Gabriel220702/Innova-TecNM-2024/COCYTED 2024/Diseño Chaleco .jpg

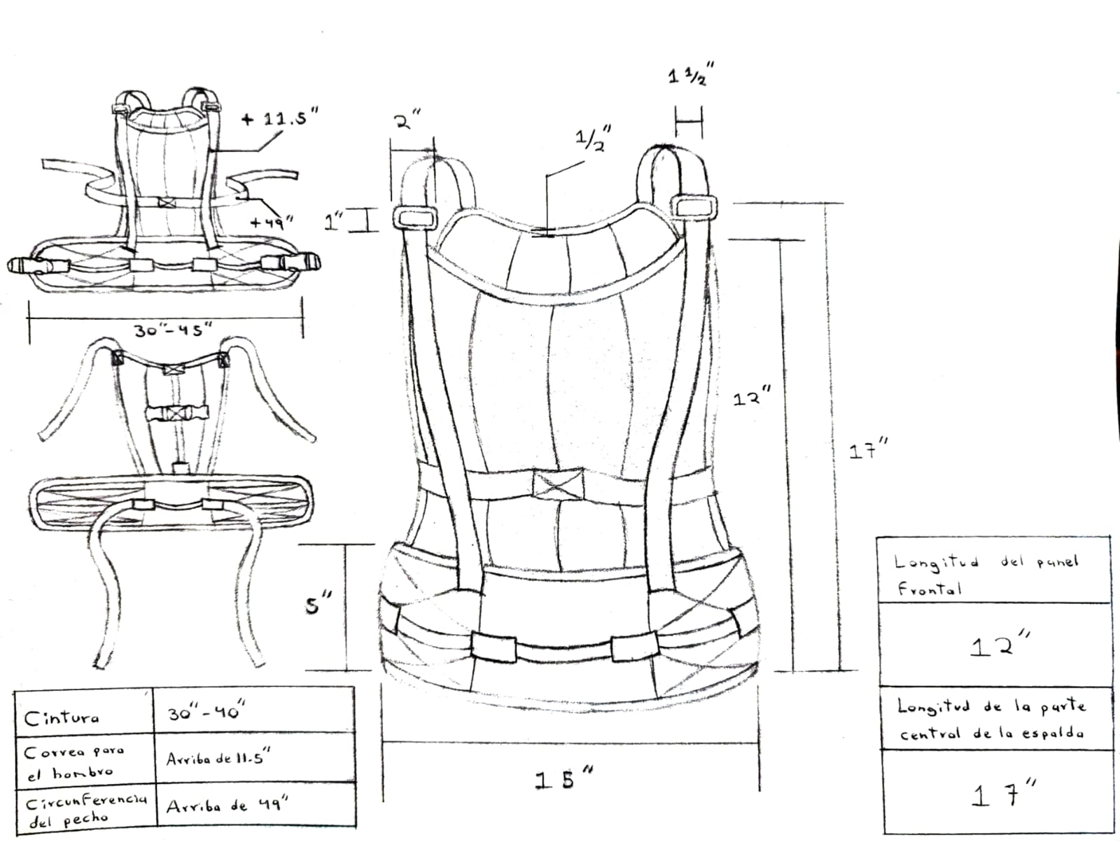
COCYTED 2024/Diseño Chaleco .jpg
