Gabriel220702/Innova-TecNM-2024/Innova TecNM 2024 Etapa Local/Imágenes/Equipo de Trabajo.png

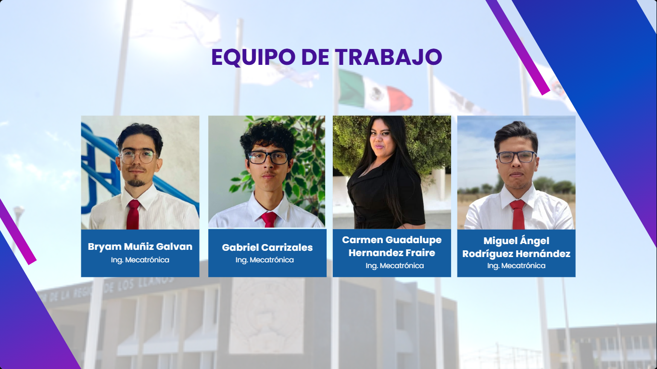
Innova TecNM 2024 Etapa Local/Imágenes/Equipo de Trabajo.png
