Gabriel220702/Innova-TecNM-2024/Innova TecNM 2024 Etapa Local/Imágenes/Estado del Arte.PNG

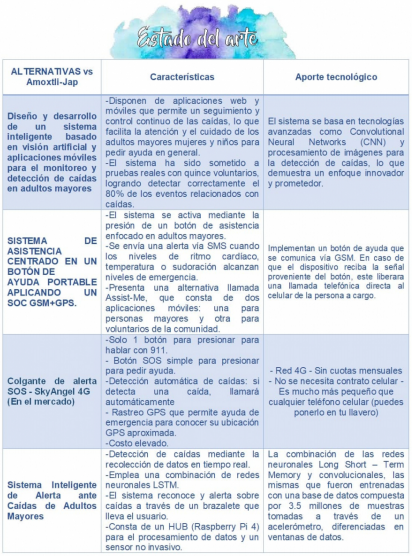
Innova TecNM 2024 Etapa Local/Imágenes/Estado del Arte.PNG
