Gabriel220702/Innova-TecNM-2024/Innova TecNM 2024 Etapa Regional/Carteles/Cartel 1.jpg

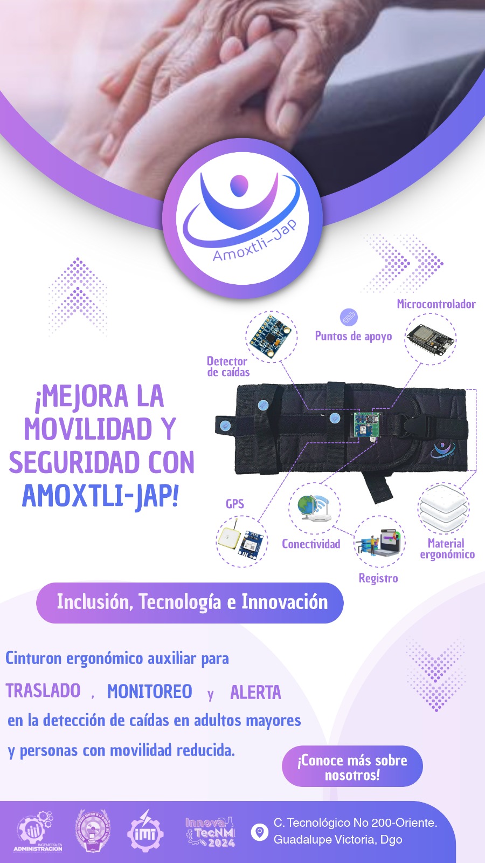
Innova TecNM 2024 Etapa Regional/Carteles/Cartel 1.jpg
