Gabriel220702/Innova-TecNM-2024/Innova TecNM 2024 Etapa Regional/Fotos, Equipo de Trabajo/Bryam.jpg

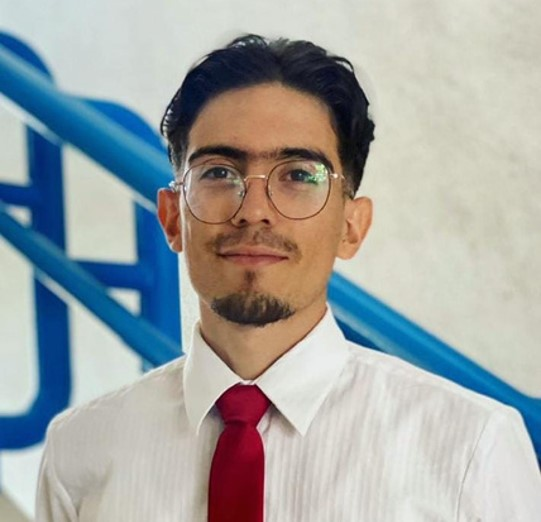
Innova TecNM 2024 Etapa Regional/Fotos, Equipo de Trabajo/Bryam.jpg
