Gabriel220702/Innova-TecNM-2024/Innova TecNM 2024 Etapa Regional/Fotos, Equipo de Trabajo/La_Abril.jpg

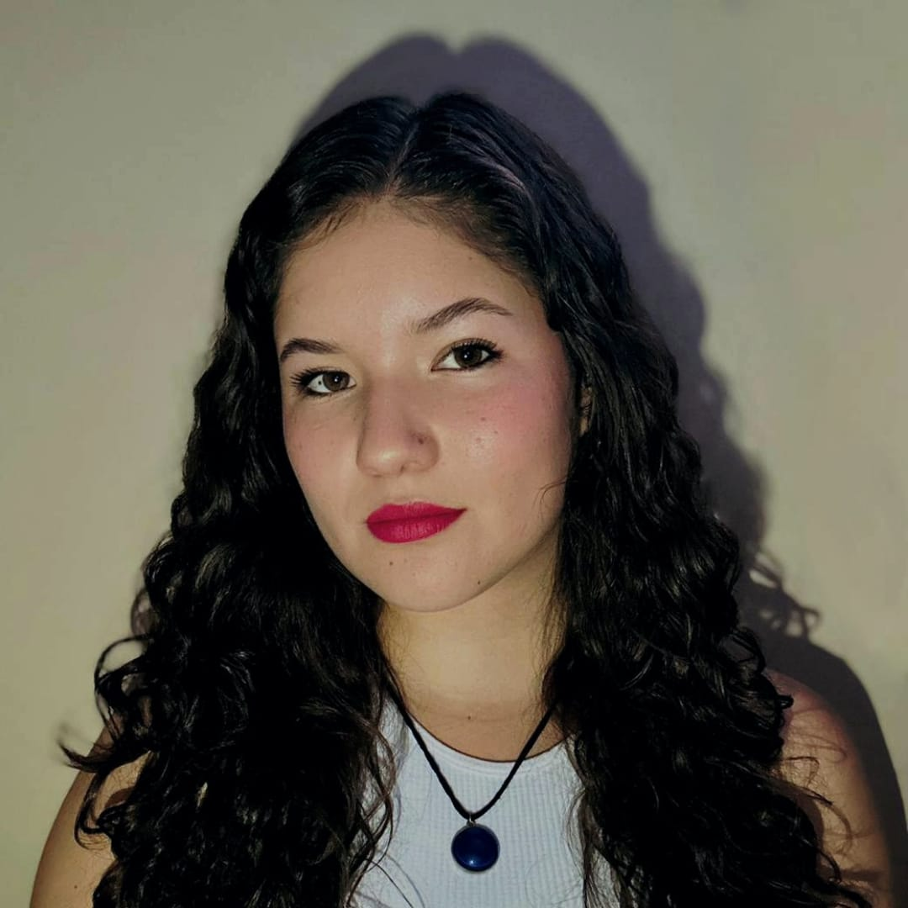
Innova TecNM 2024 Etapa Regional/Fotos, Equipo de Trabajo/La_Abril.jpg
