Gabriel220702/Innova-TecNM-2024/Innova TecNM 2024 Etapa Regional/Galeria de Imagenes, Página Web/Abuelita con Chaleco 3.jpg

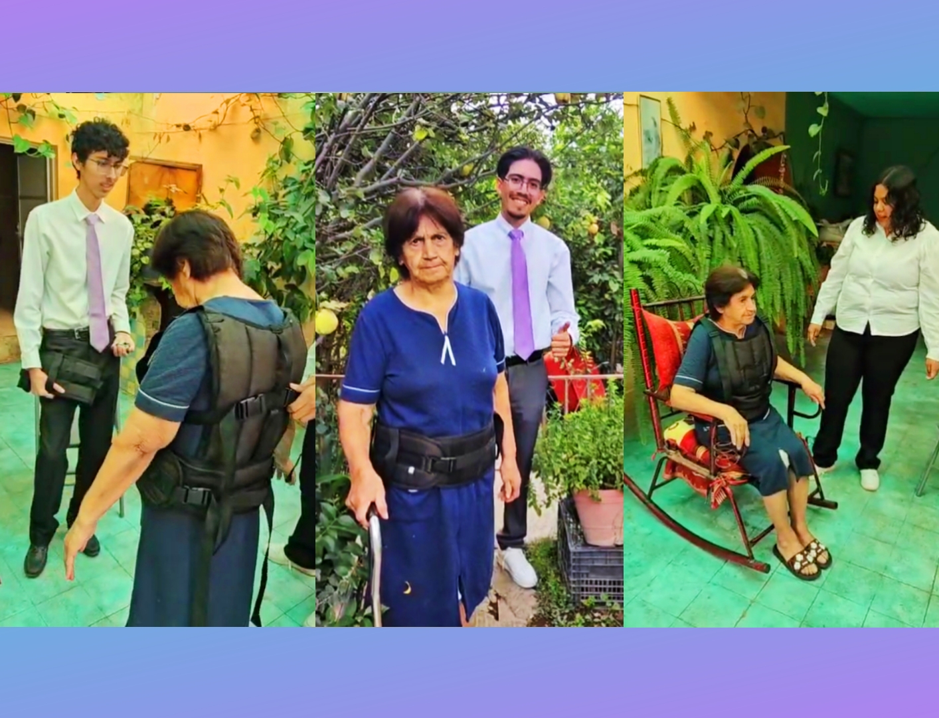
Innova TecNM 2024 Etapa Regional/Galeria de Imagenes, Página Web/Abuelita con Chaleco 3.jpg
