Gabriel220702/Innova-TecNM-2024/Innova TecNM 2024 Etapa Regional/Galeria de Imagenes, Página Web/Cinturón y Chaleco.jpg

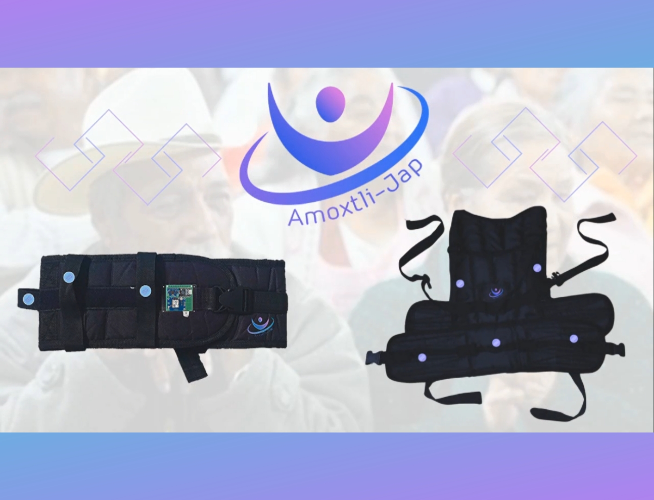
Innova TecNM 2024 Etapa Regional/Galeria de Imagenes, Página Web/Cinturón y Chaleco.jpg
