Gabriel220702/Innova-TecNM-2024/Innova TecNM 2024 Etapa Regional/Galeria de Imagenes, Página Web/Panel de Control.jpg

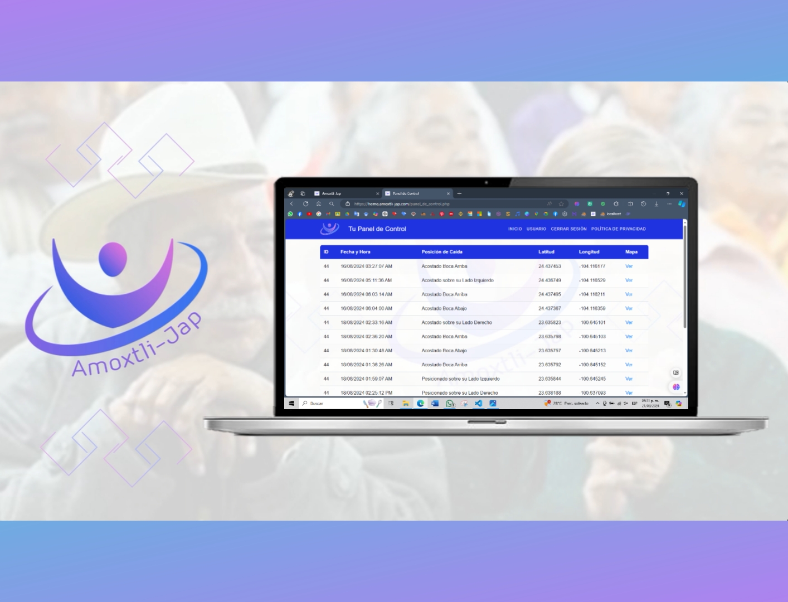
Innova TecNM 2024 Etapa Regional/Galeria de Imagenes, Página Web/Panel de Control.jpg
