Gabriel220702/Innova-TecNM-2024/Innova TecNM 2024 Etapa Regional/Galeria de Imagenes, Página Web/WhatsApp y Google Maps.jpg

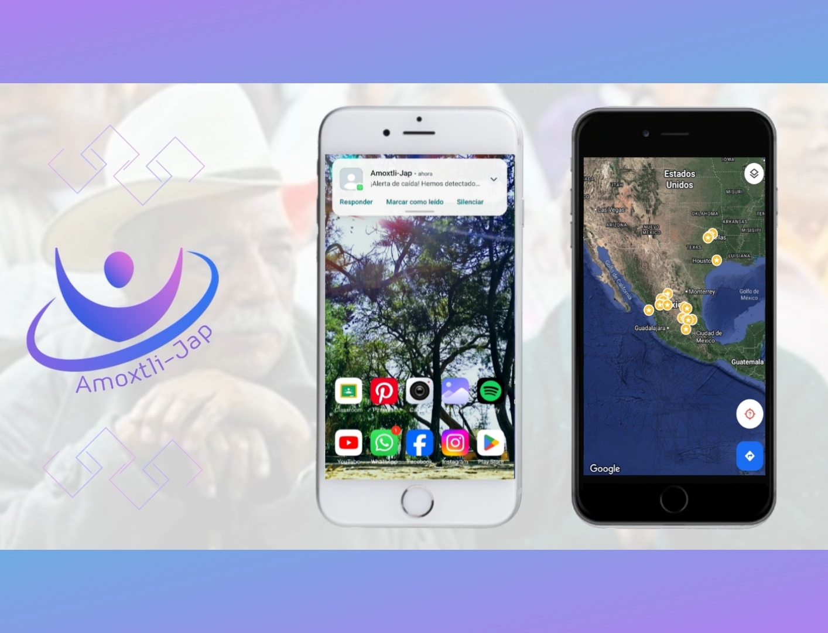
Innova TecNM 2024 Etapa Regional/Galeria de Imagenes, Página Web/WhatsApp y Google Maps.jpg
