Gabriel220702/Innova-TecNM-2024/Innova TecNM 2024 Etapa Regional/Imágenes, Información con Diseño/Cuantificación de Personal.png

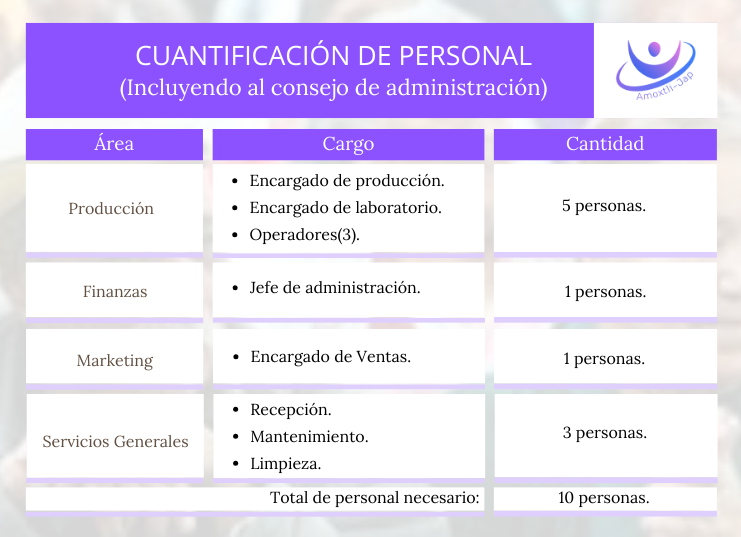
Innova TecNM 2024 Etapa Regional/Imágenes, Información con Diseño/Cuantificación de Personal.png
