Gabriel220702/Innova-TecNM-2024/Innova TecNM 2024 Etapa Regional/Imágenes, Información con Diseño/Descripción de la Innovación.png

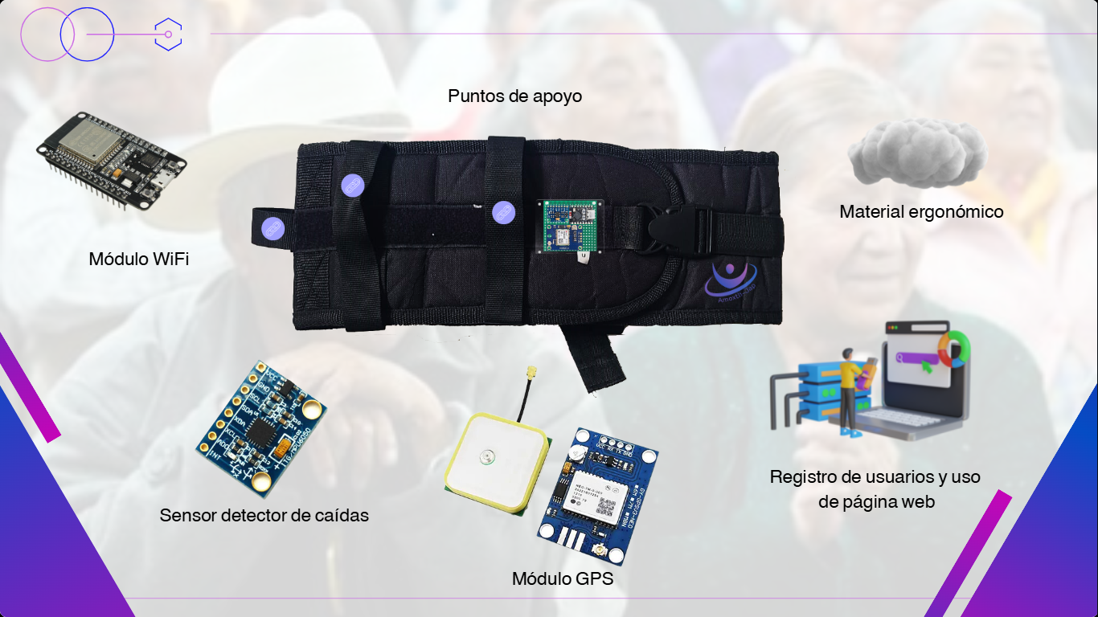
Innova TecNM 2024 Etapa Regional/Imágenes, Información con Diseño/Descripción de la Innovación.png
