Gabriel220702/Innova-TecNM-2024/Innova TecNM 2024 Etapa Regional/Imágenes, Información con Diseño/Equipo de Trabajo.png

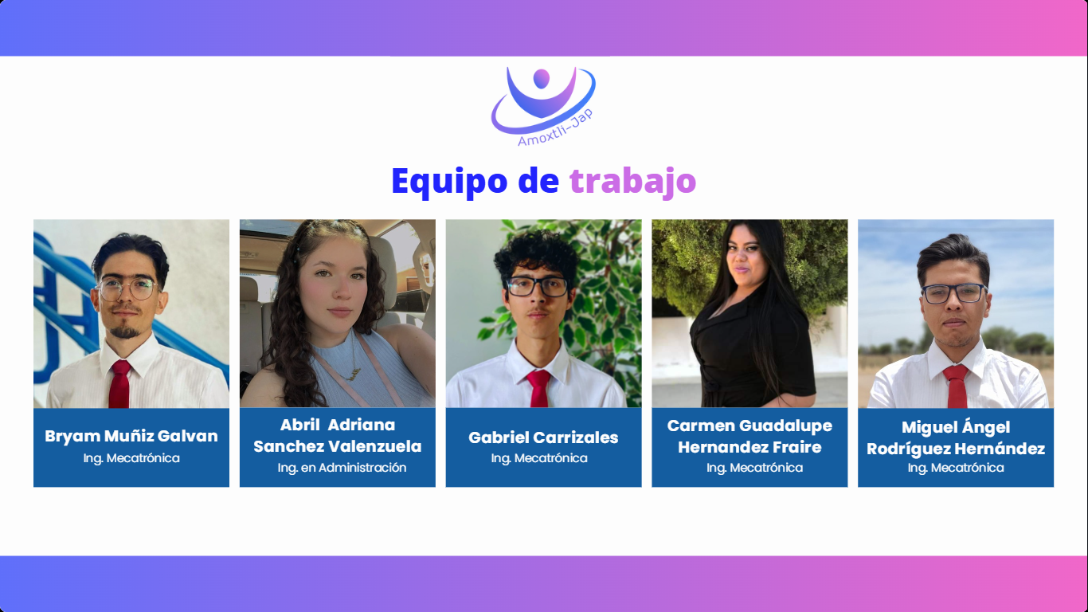
Innova TecNM 2024 Etapa Regional/Imágenes, Información con Diseño/Equipo de Trabajo.png
