Gabriel220702/Innova-TecNM-2024/Innova TecNM 2024 Etapa Regional/Imágenes, Información con Diseño/Flujo de Efectivo Proyectado.png

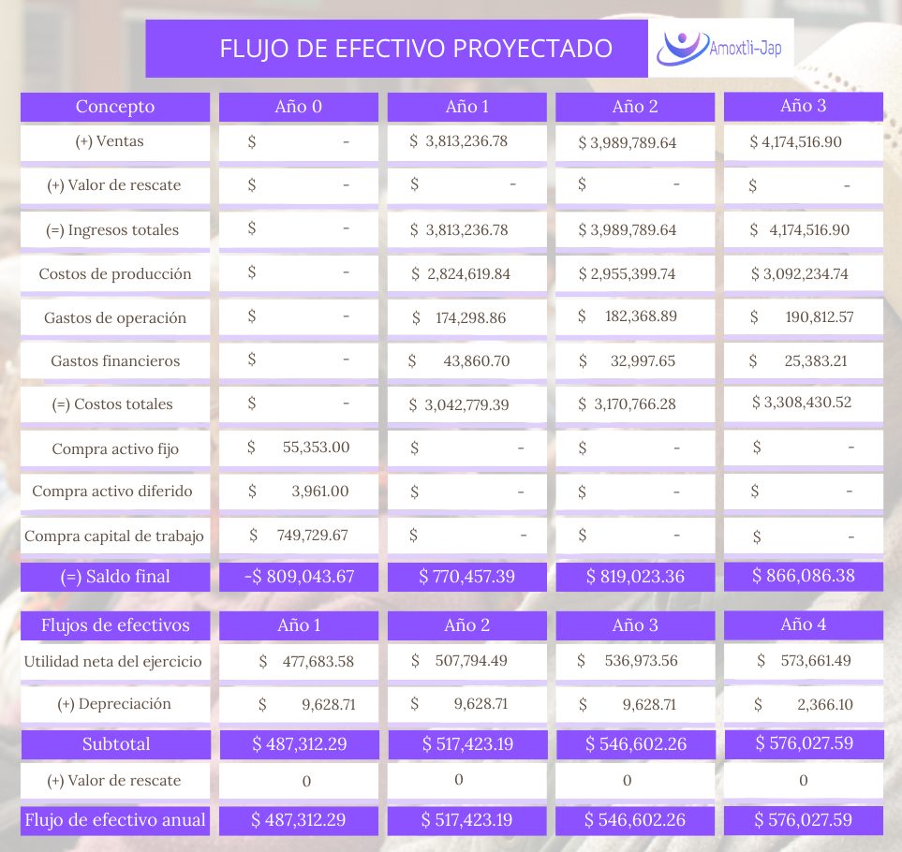
Innova TecNM 2024 Etapa Regional/Imágenes, Información con Diseño/Flujo de Efectivo Proyectado.png
