Gabriel220702/Innova-TecNM-2024/Innova TecNM 2024 Etapa Regional/Imágenes, Información con Diseño/FODA.png

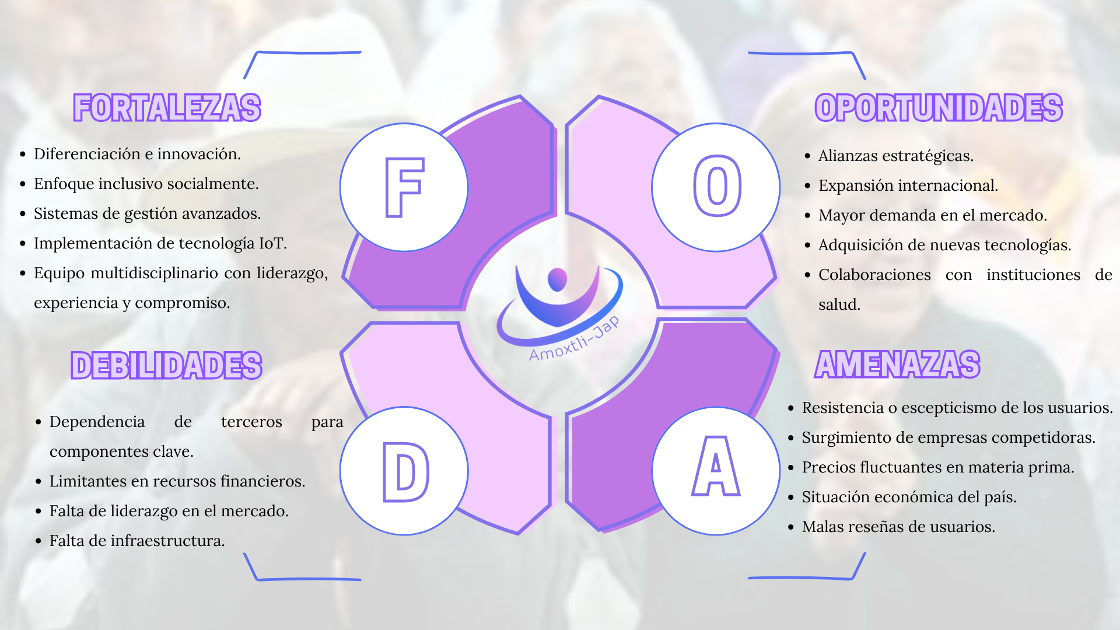
Innova TecNM 2024 Etapa Regional/Imágenes, Información con Diseño/FODA.png
