Gabriel220702/Innova-TecNM-2024/Innova TecNM 2024 Etapa Regional/Página Web/img/Amoxtli_fondo.jpg

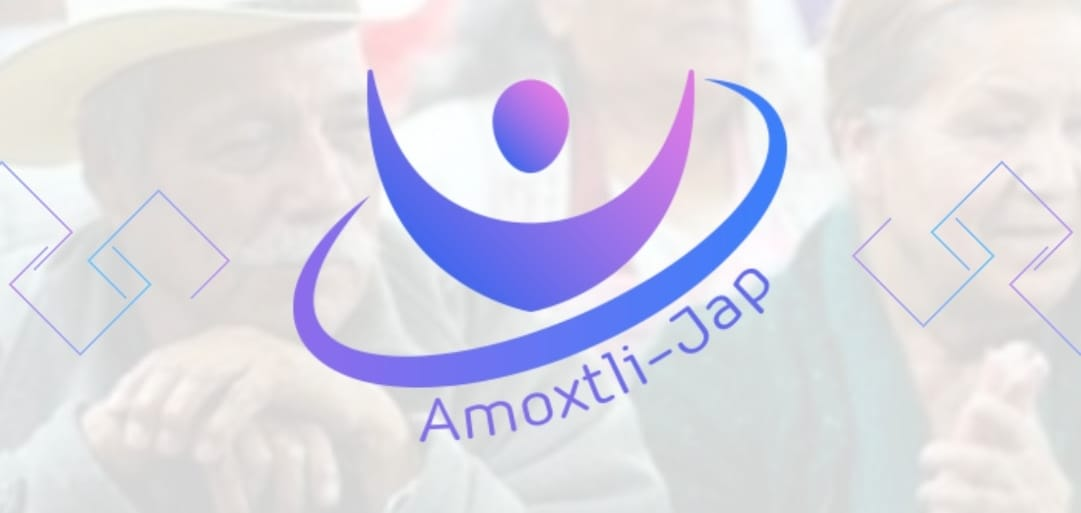
Innova TecNM 2024 Etapa Regional/Página Web/img/Amoxtli_fondo.jpg
