Gabriel220702/Innova-TecNM-2024/Innova TecNM 2024 Etapa Regional/Página Web/img/Descripción.png

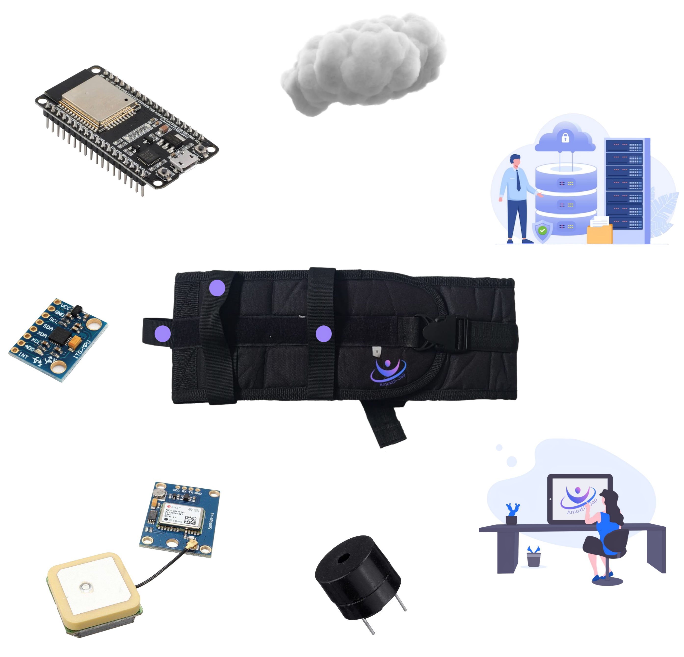
Innova TecNM 2024 Etapa Regional/Página Web/img/Descripción.png
