Gabriel220702/Innova-TecNM-2024/Innova TecNM 2024 Etapa Regional/Página Web/img/Fondo_Formulario.jpg

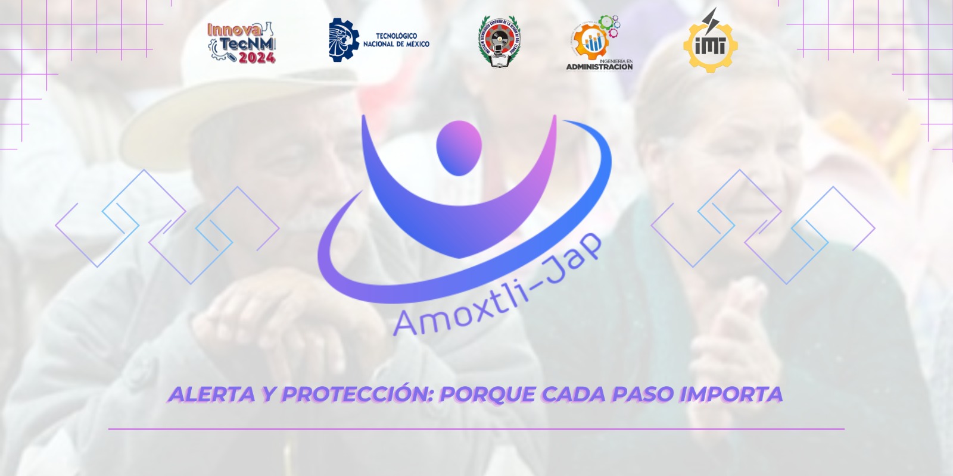
Innova TecNM 2024 Etapa Regional/Página Web/img/Fondo_Formulario.jpg
