Gabriel220702/Innova-TecNM-2024/Innova TecNM 2024 Etapa Regional/Página Web/img/portfolio/Abuelita con Cinturón.jpg

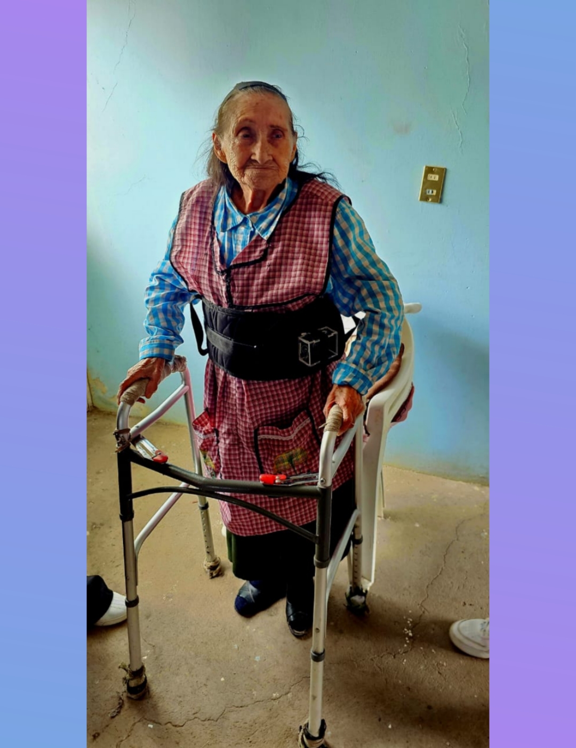
Innova TecNM 2024 Etapa Regional/Página Web/img/portfolio/Abuelita con Cinturón.jpg
