Gabriel220702/Innova-TecNM-2024/Innova TecNM 2024 Etapa Regional/Página Web/img/portfolio/Cinturon_info2.jpg

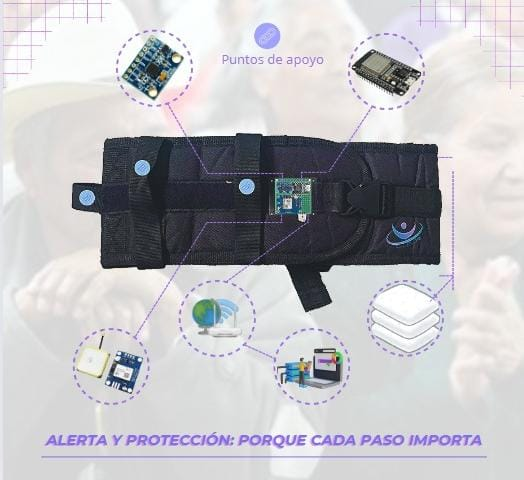
Innova TecNM 2024 Etapa Regional/Página Web/img/portfolio/Cinturon_info2.jpg
