Gabriel220702/Innova-TecNM-2024/Innova TecNM 2024 Etapa Regional/Página Web/img/portfolio/sensor1.jpg

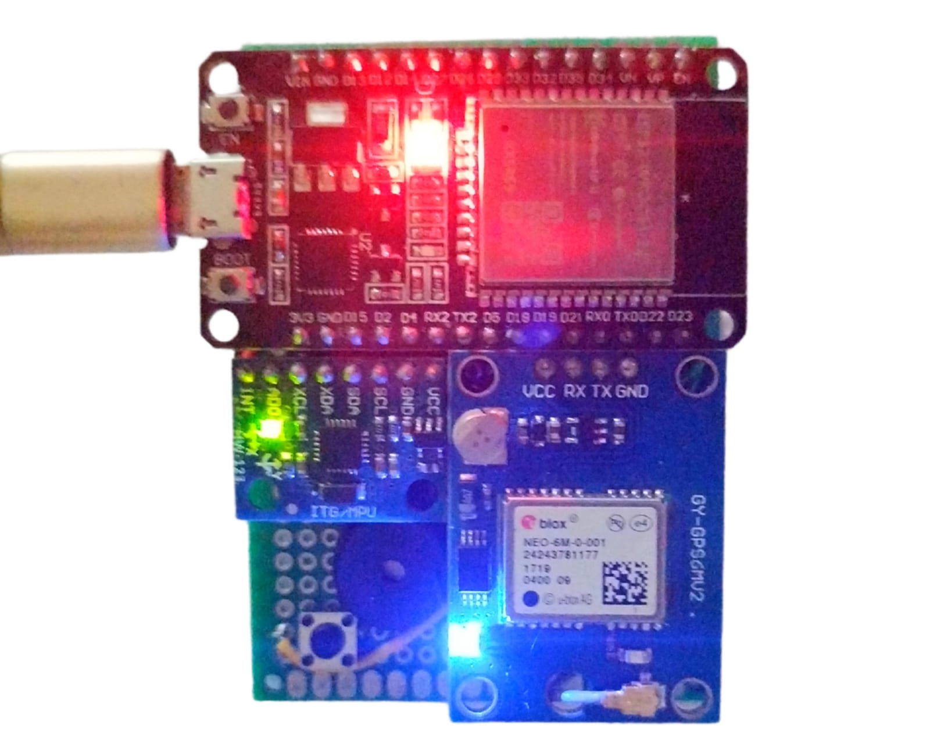
Innova TecNM 2024 Etapa Regional/Página Web/img/portfolio/sensor1.jpg
