Gabriel220702/Innova-TecNM-2024/Innova TecNM 2024 Etapa Regional/Página Web/SignIn_SignUp/img/Compu.png

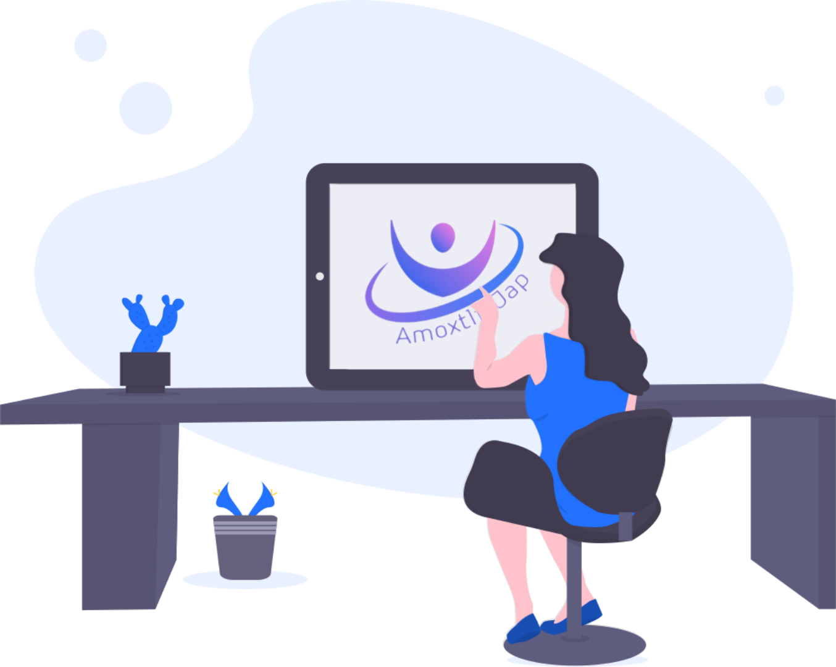
Innova TecNM 2024 Etapa Regional/Página Web/SignIn_SignUp/img/Compu.png
